vishnuprasathmohanrajsubbulakshmi/Design-of-a-Transimpedance-Amplifier-for-Photodiodes/Draft1.asc

C1: cap; 580p
C2: cap; 32p
C3: cap; 1µ
G1: g; 1
G2: g; 1
I1: current; 0; AC 1
I2: current; 0.02p; AC 6p
I3: current; 0.02p
R1: res; 1.25G
R2: res; 100
R3: res; 50Meg
R4: res; 50Meg
R5: Res; 3.62e-8
R7: Res; 9.8e-10
U2: LMC6482A
V1: voltage; 0.11m; AC 3.7m
V2: voltage; 6.5
V3: voltage; -2.5
V4: voltage; 0
Named nets: 0, pos, vgr, neg, Vou, noise_BPW, noise_SFH
.ac dec 0 10 1000k
.dc I1 0 200n 100p
.noise V(Vou) I1 dec 10 1 10k
.measure noise NOISERMS integ V(onoise) 1 to 10k
